tim-clifford/ErgoDash/MCAD/parts-step/CEN979012RO2_Kailh_Red_Encoder_9mm.step

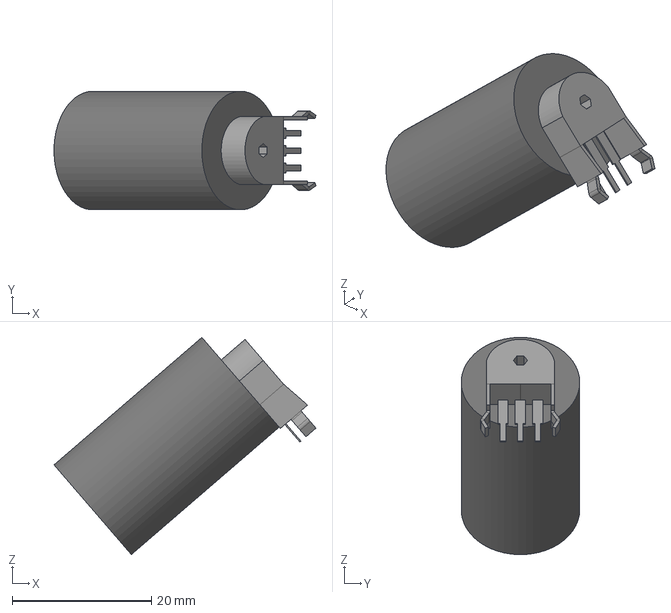
[picture p19: CAD file, 2020-12-29]
MCAD/parts-step/CEN979012RO2_Kailh_Red_Encoder_9mm.step
37.6 x 17.0 x 31.2 mm
CEN979012RO2_Kailh_Red_Encoder_9mm
Knob
